cracked-machine/MIDIPresetController/HW/res/img/MIDIPresetController.pdf

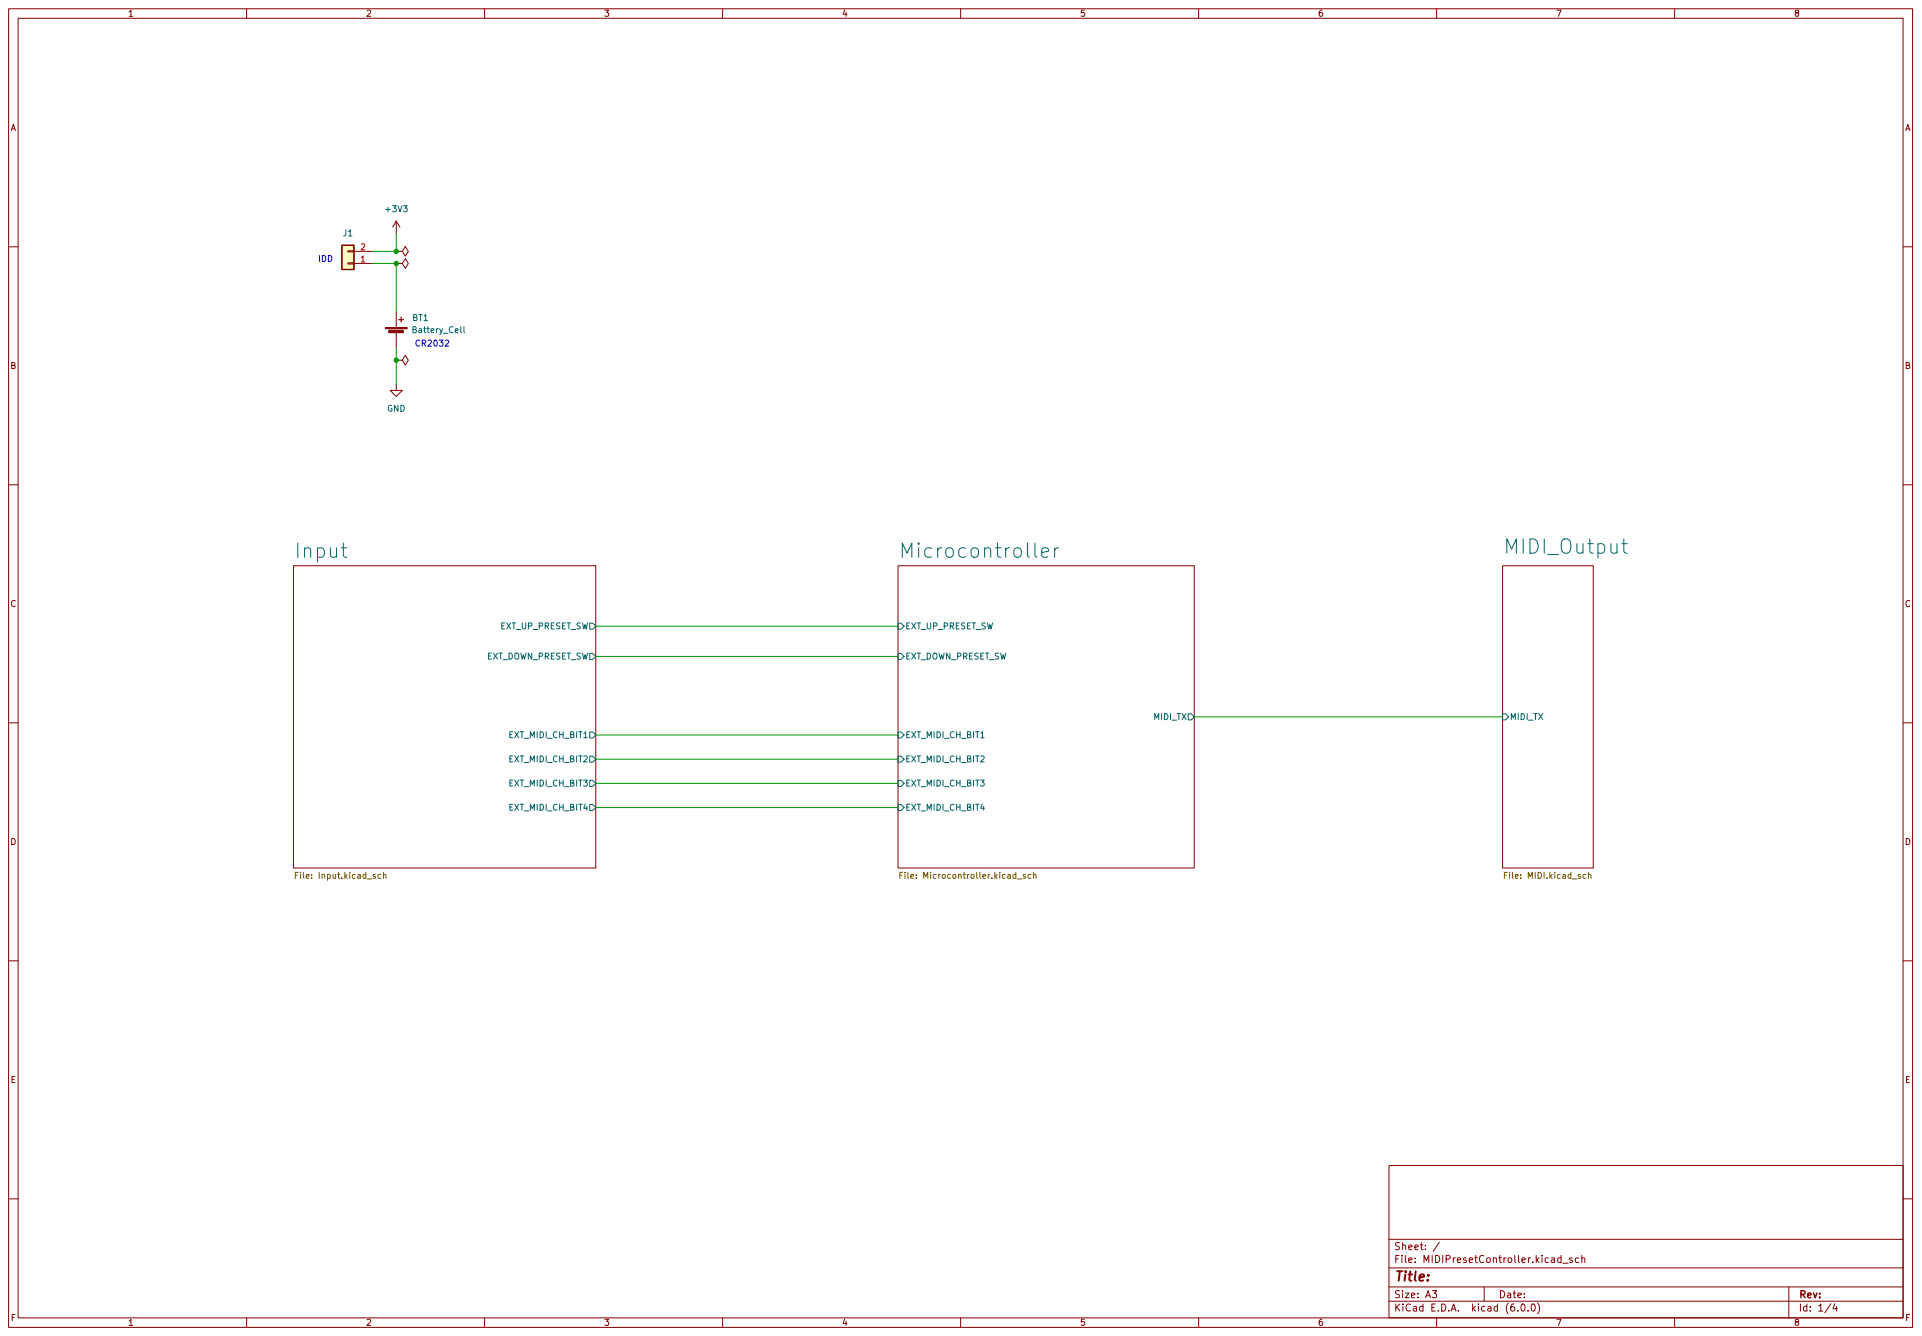
[picture p11: page 1]

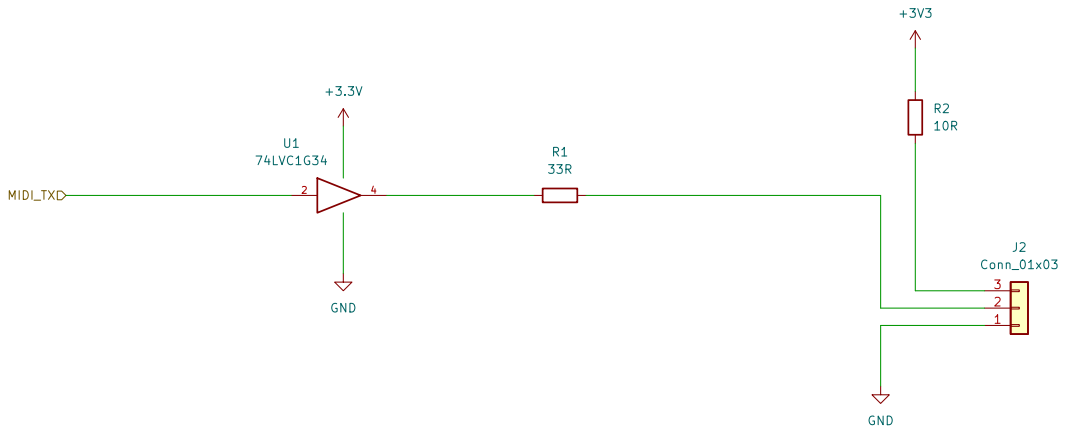
[picture p12: page 2]

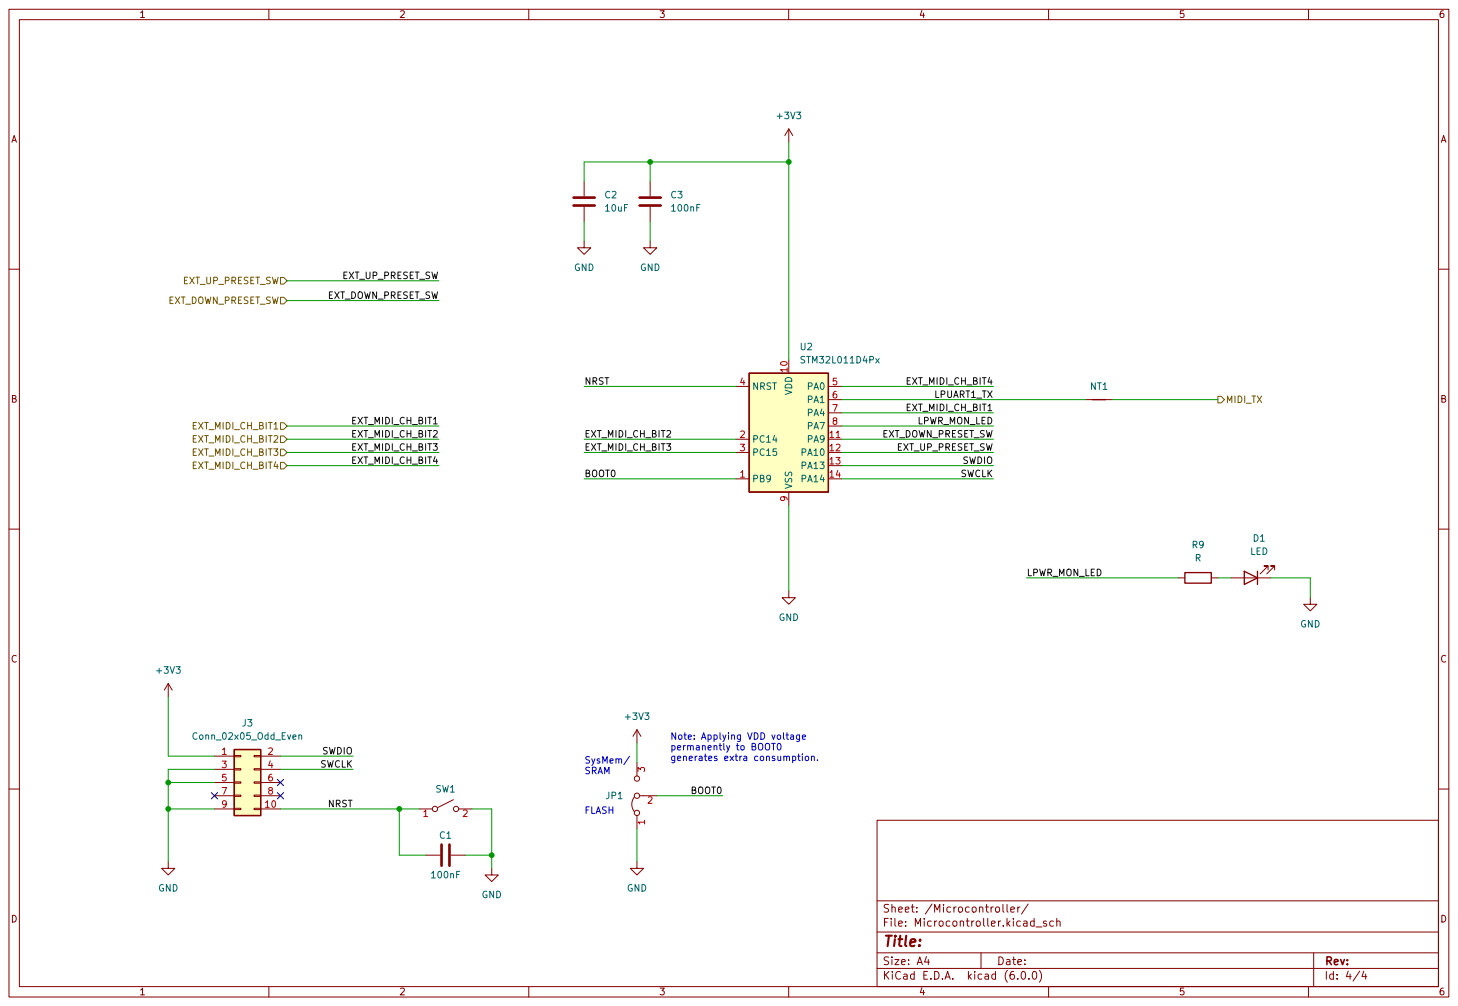
[picture p13: page 3]

Note: Applying VDD voltage
permanently to BOOT0

File: Microcontroller.kicad_sch Sheet: /Microcontroller/
Id: 4/4 Title:

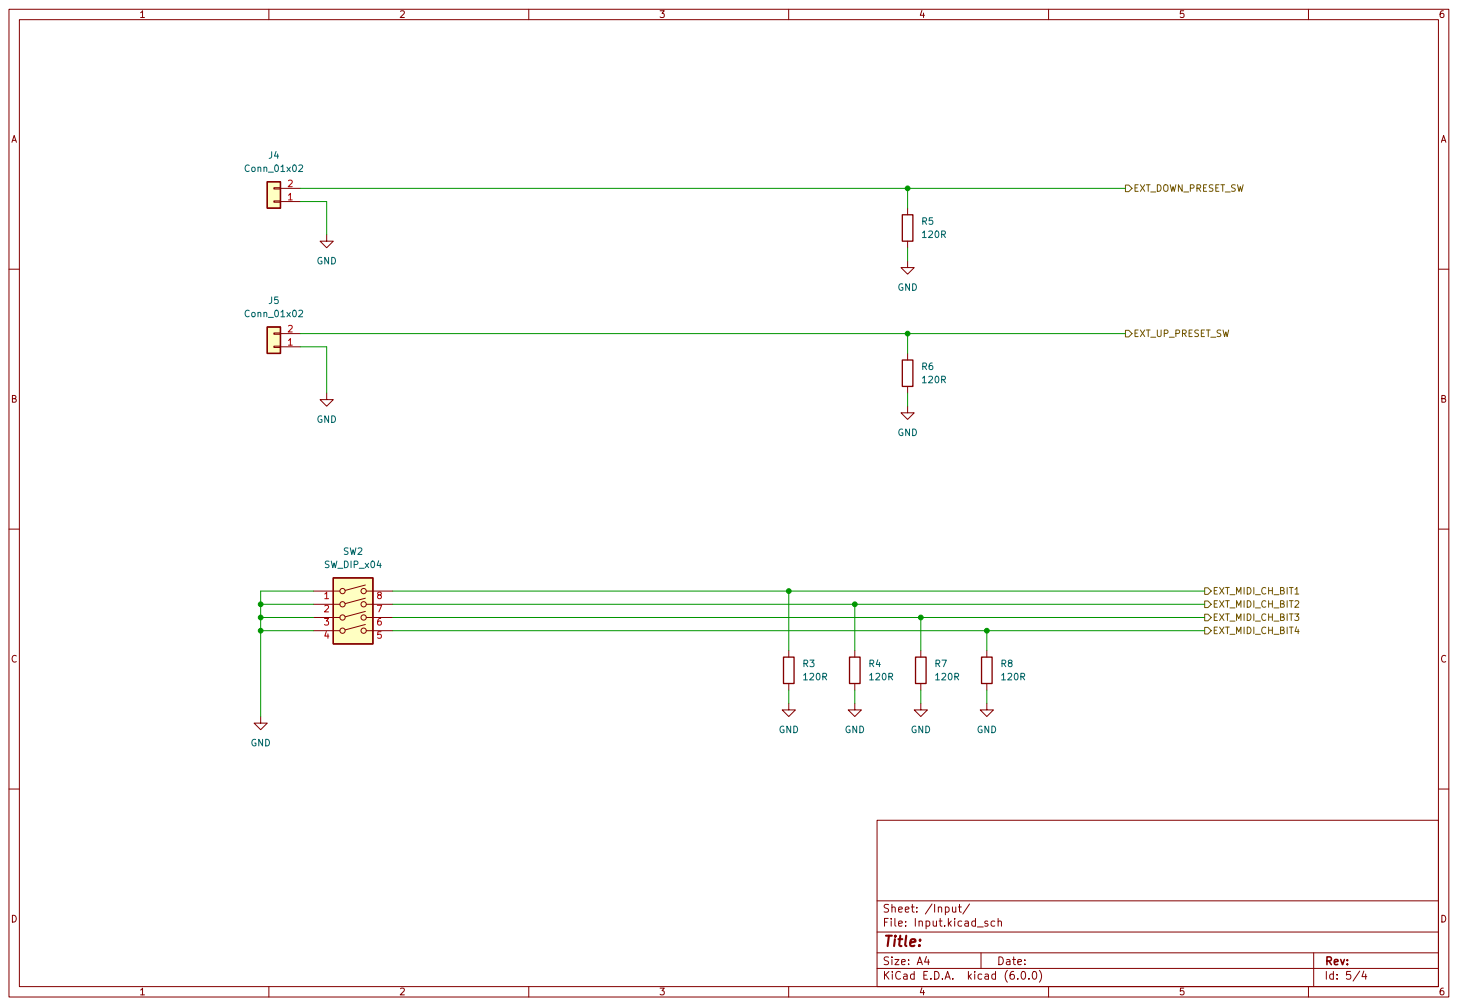
[picture p14: page 4]
